tenox7/tenoxvga/eagle/ECL2VGA_RevF.1.sch

## EAGLE design eagle/ECL2VGA_RevF.1.sch (2016-02-01)

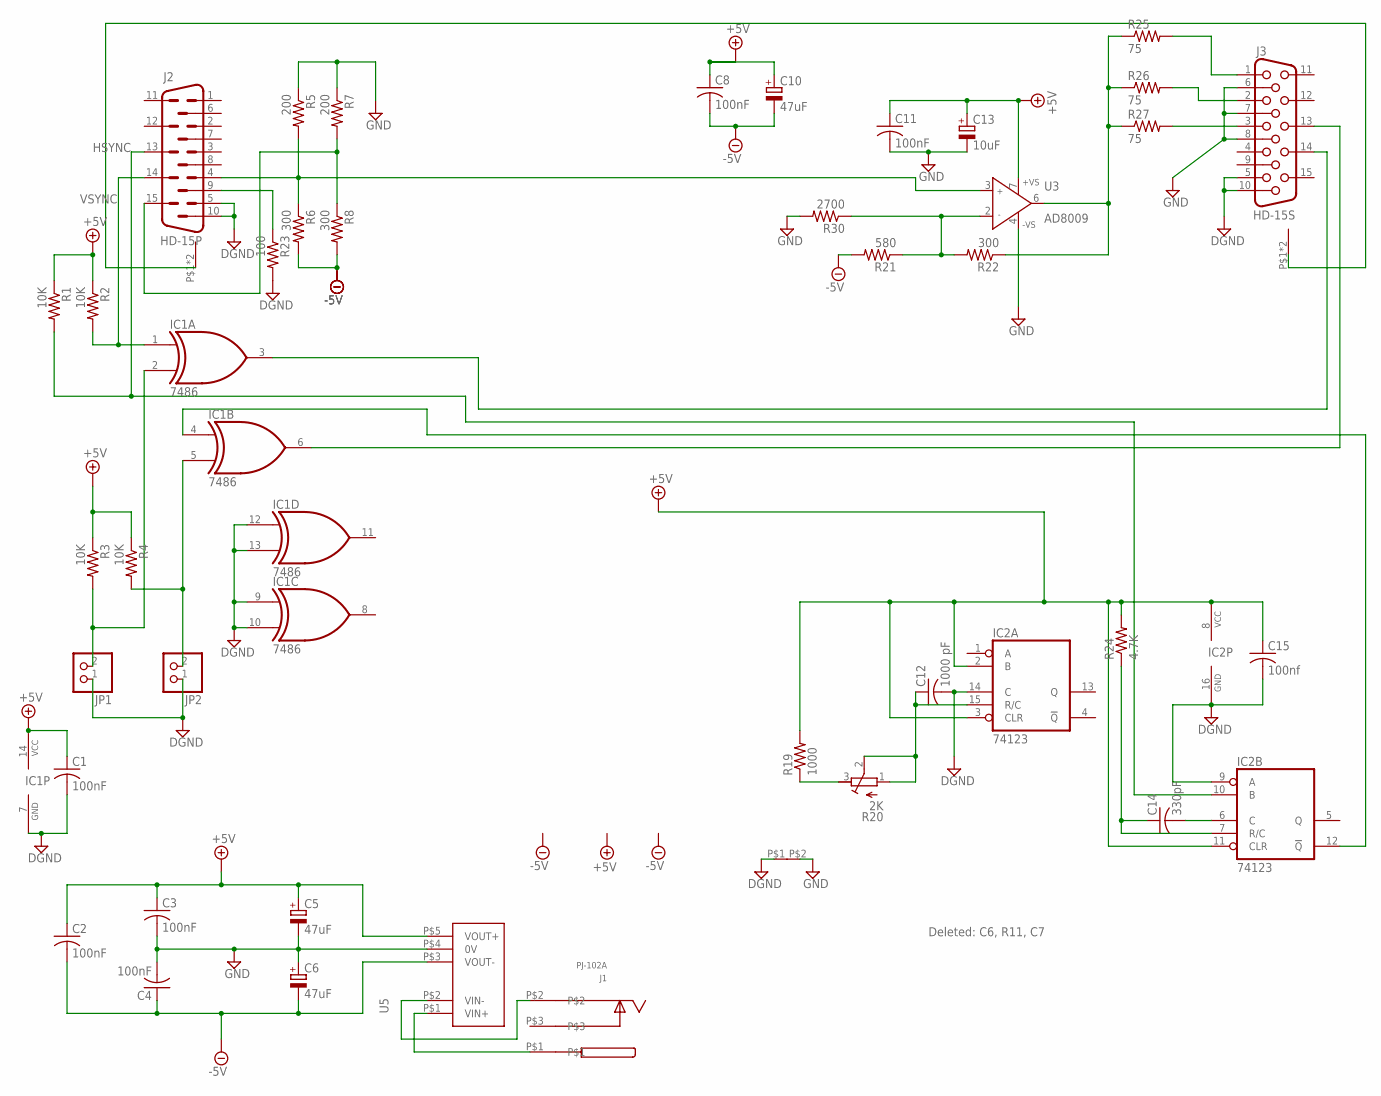
[picture p6: schematic ECL2VGA_RevF.1.sch]

Parts:
C1, C2, C3, C4, C8, C11: 100nF; C0805
C5, C6, C10: 47uF; CT6032
C12: 1000 pF; C0805
C13: 10uF; CT6032
C14: 330pF; C0805
C15: 100nf; C0805
IC1: 7486; TSSOP14
IC2: 74123; TSSOP16
J1: PJ-102A
J2: HD-15P; HDM15H
J3: HD-15S; HDF15H
JP1, JP2: PINHD-1X2; 1X02
R1, R2, R3, R4: 10K; R0805
R5, R7: 200; R0805
R6, R8, R22: 300; R0805
R19: 1000; R0805
R20: 2K; RTRIM64W
R21: 580; R0805
R23: 100; R0805
R24: 4.7K; R0805
R25, R26, R27: 75; R0805
R30: 2700; R0805
U3: AD8009; SOIC8
U5: MEJ2-5_0_+5; MEJ2
U$1: TRACE

Connections:
0V: C2.2, C4.1, C6.-, C8.2, C10.-, R6.2, R8.2, U5.P$3 (VOUT-)
+5V: C1.1, C2.1, C3.1, C5.+, C8.1, C10.+, C11.1, C13.+, C15.1, IC1.14 (VCC), IC2.2 (B), IC2.3 (CLR), IC2.8 (VCC), IC2.11 (CLR), R1.1, R2.1, R3.1, R4.1, R19.2, R24.2, U3.7 (+VS), U5.P$5 (VOUT+)
-5V: R21.2
DGND: C1.2, C12.2, C15.2, IC1.7 (GND), IC1.9 (I0), IC1.10 (I1), IC1.12 (I0), IC1.13 (I1), IC2.9 (A), IC2.14 (C), IC2.16 (GND), J2.5, J2.10, J3.5, J3.10, JP1.1, JP2.1, R23.2, U$1.P$1
ECL_H: J2.4, R5.2, R6.1, U3.3 (IN+)
ECL_L: J2.15, R7.2, R8.1
GND: C3.2, C4.2, C5.-, C6.+, C11.2, C13.-, J3.6, J3.7, J3.8, R5.1, R7.1, R30.2, U3.4 (-VS), U5.P$4 (0V), U$1.P$2
unnamed: J3.1, R25.2
unnamed: J3.2, R26.2
unnamed: J3.3, R27.2
unnamed: IC1.3 (O), J3.14
unnamed: IC1.6 (O), J3.13
unnamed: R21.1, R22.2, R30.1, U3.2 (IN-)
unnamed: R22.1, R25.1, R26.1, R27.1, U3.6 (OUT)
unnamed: IC1.5 (I1), JP2.2, R4.2
unnamed: J2.13, R1.2
unnamed: IC1.1 (I0), J2.14, R2.2
unnamed: IC1.4 (I0), IC2.12 (!Q)
unnamed: IC1.2 (I1), JP1.2, R3.2
unnamed: C14.1, IC2.7 (R/C), R24.1
unnamed: C14.2, IC2.6 (C)
unnamed: J2.9, R23.1
unnamed: C12.1, IC2.15 (R/C), R20.1 (E), R20.2 (S)
unnamed: R19.1, R20.3 (A)
unnamed: J1.P$1, U5.P$1 (VIN+)
unnamed: J1.P$2, U5.P$2 (VIN-)
SHEILD: J2.P$1 (16), J3.P$1 (16)

Notes on the sheet:
HSYNC
VSYNC
Deleted: C6, R11, C7
